Gaboze-Pocaio/Round-1/silks/eagleUp_GabozePocaio_board_bottom.png

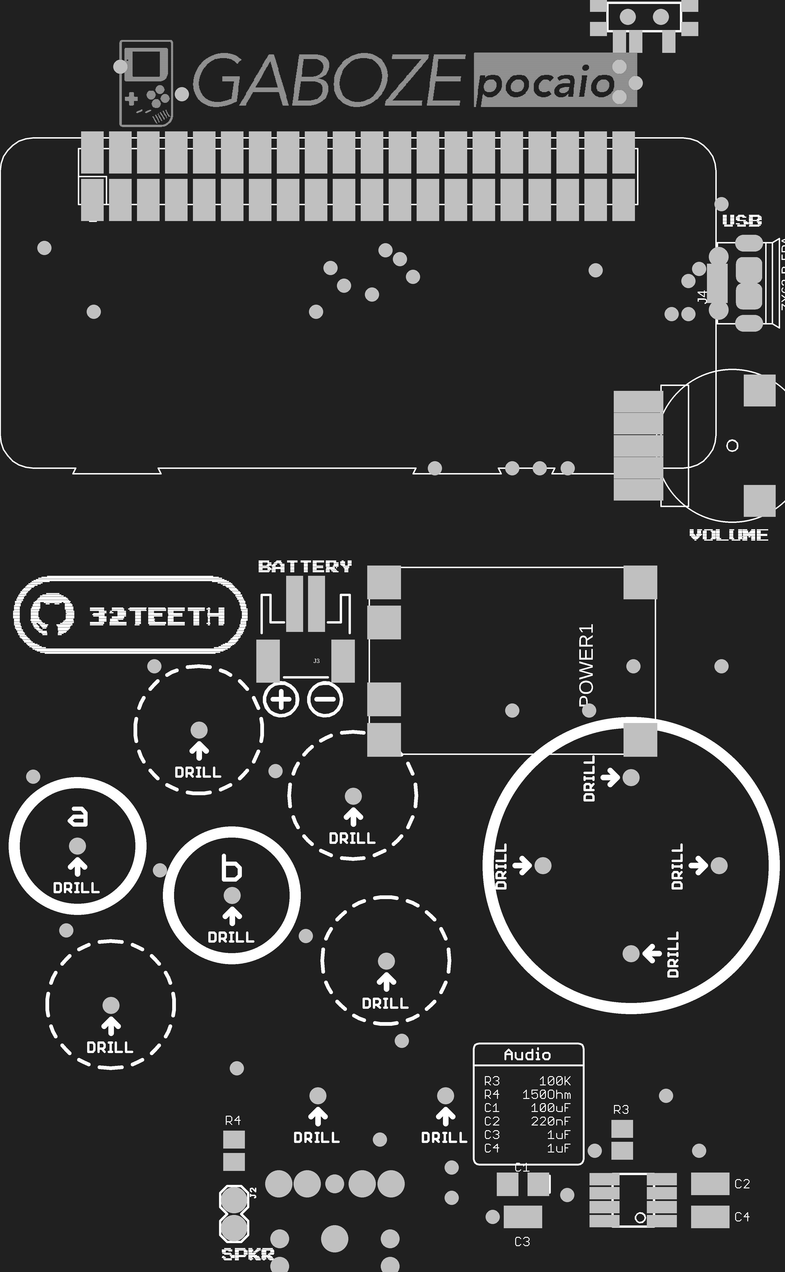
silks/eagleUp_GabozePocaio_board_bottom.png
