Gaboze-Pocaio/Round-1/silks/eagleUp_GabozePocaio_board_top.png

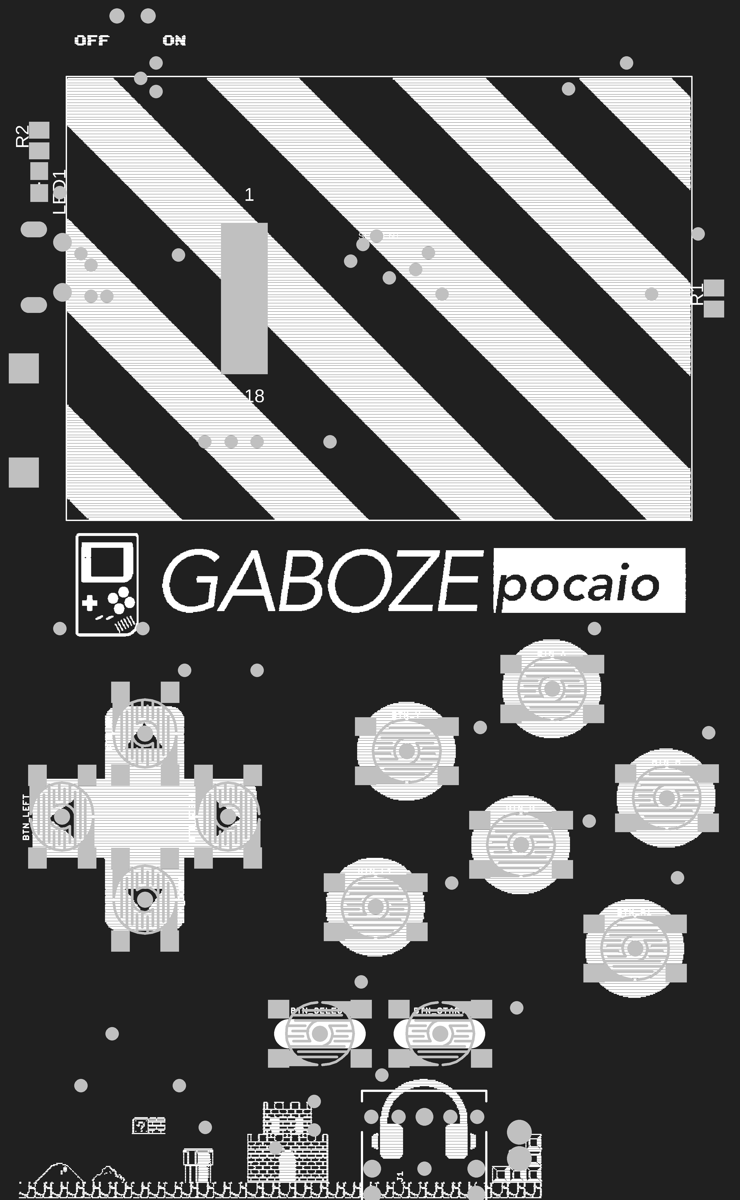
silks/eagleUp_GabozePocaio_board_top.png
