Gaboze-Pocaio/Round-1/silks/eagleUp_gameboy-pocket_board_bottom.png

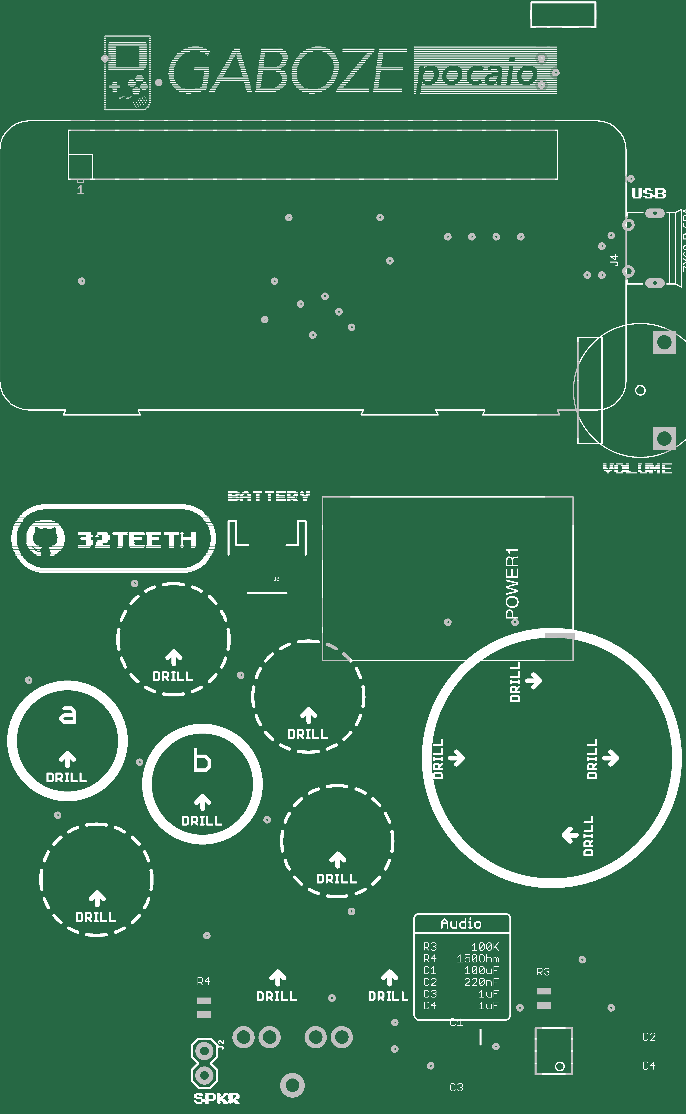
silks/eagleUp_gameboy-pocket_board_bottom.png
