Gaboze-Pocaio/Round-1/theme/retropie_art.png

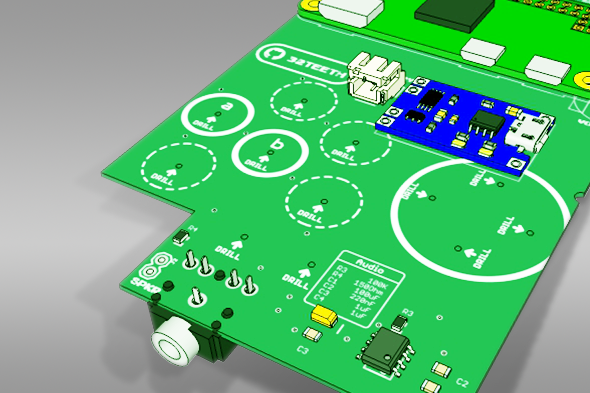
theme/retropie_art.png
