Gaboze-Pocaio/Round-1/theme/retropie_art_blur.png

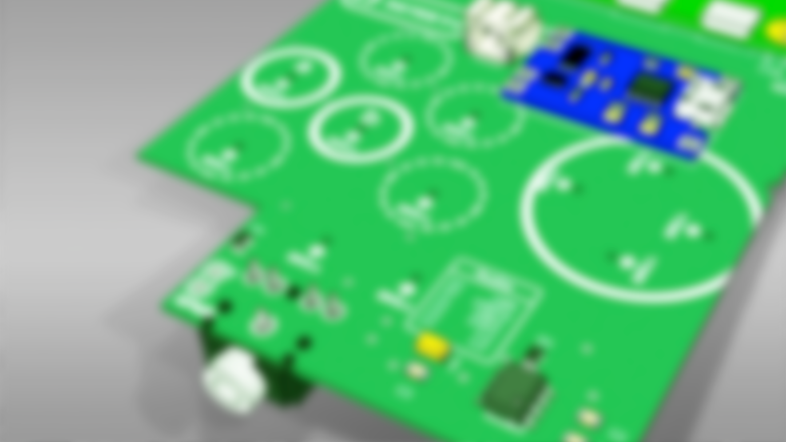
theme/retropie_art_blur.png
